foostan/crkbd/pcbs/common/right.kicad_sch

## KiCad design pcbs/common/right.kicad_sch (2024-05-06)

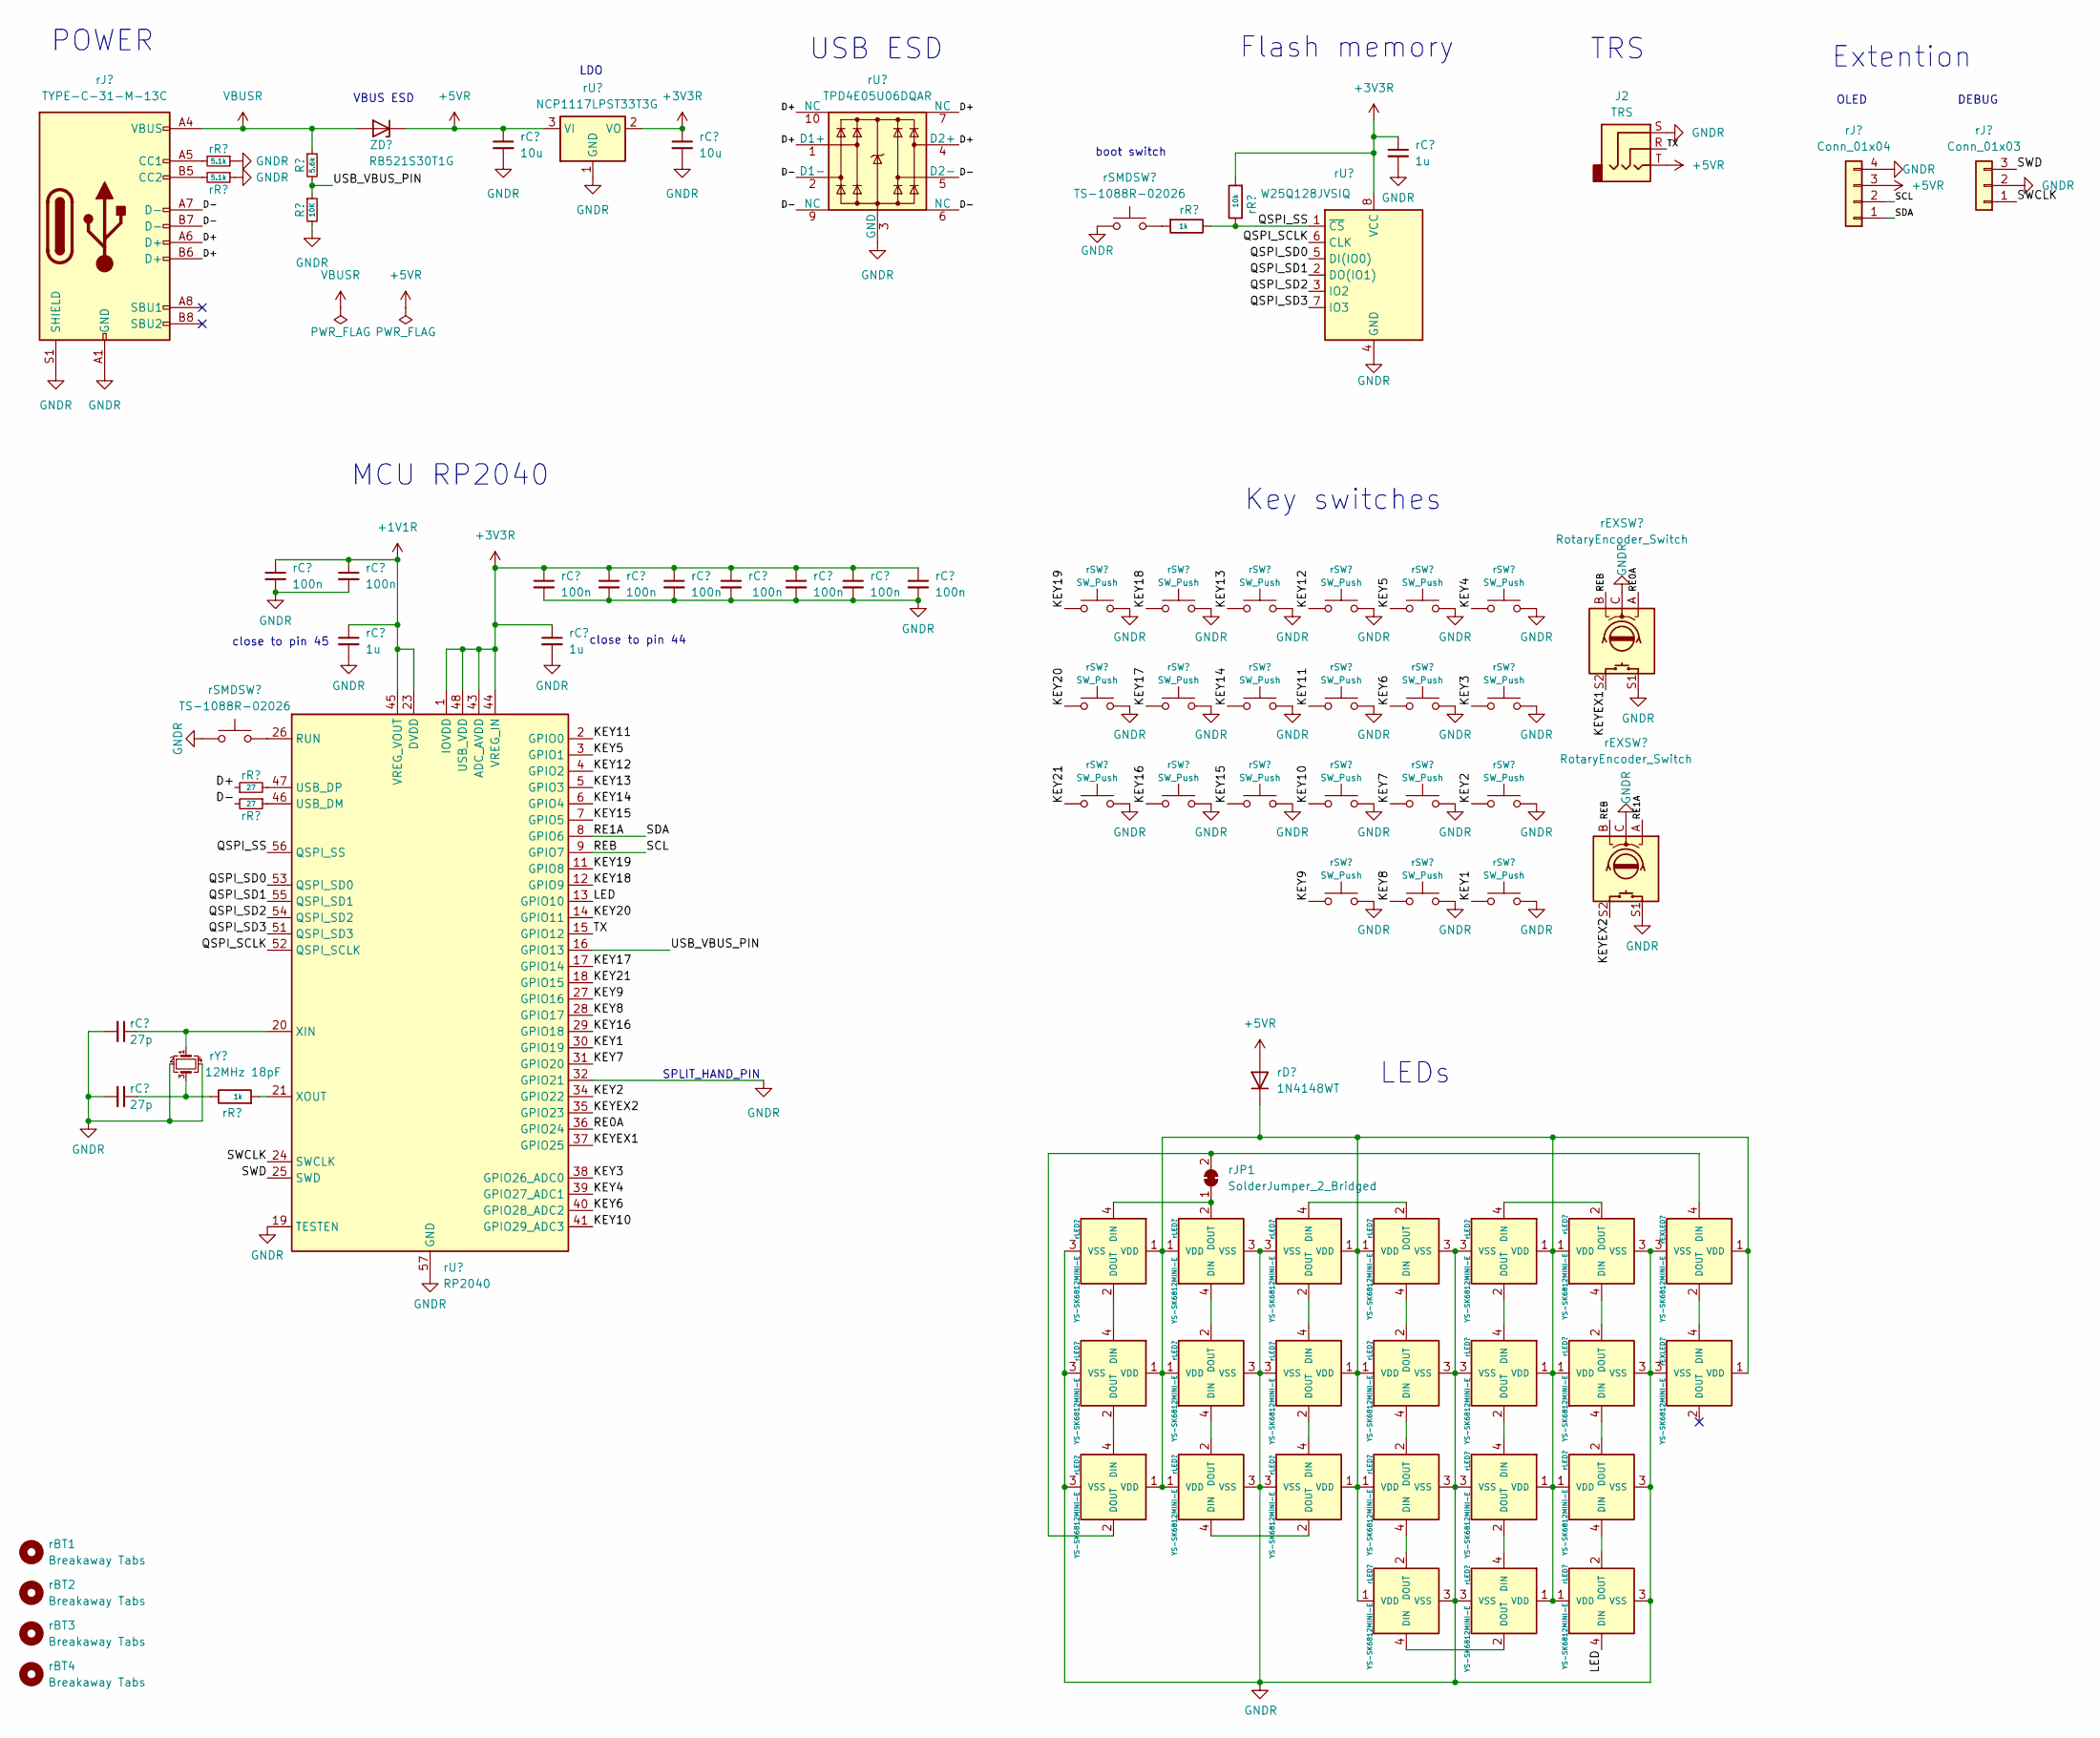
[picture p46: schematic right.kicad_sch]

Parts:
J2: TRS; PJ-398A-5A_PJ-399B-6A; JLCPCB Part # C128994
R8: 5.6k; R_0402_1005Metric
R9: 10K; R_0402_1005Metric
ZD1: RB521S30T1G; D_SOD-523; JLCPCB Part # C145179
rBT1, rBT2, rBT3, rBT4: Breakaway Tabs; Breakaway_Tabs
rC1, rC2: 27p; C_0402_1005Metric
rC3, rC4, rC7, rC9, rC10, rC12, rC13, rC14, rC15: 100n; C_0402_1005Metric
rC5, rC8, rC16: 1u; C_0402_1005Metric
rC6, rC11: 10u; C_0402_1005Metric
rD1: 1N4148WT; D_SOD-523; JLCPCB Part # C232841
rEXLED1, rEXLED2: YS-SK6812MINI-E
rEXSW1, rEXSW2: RotaryEncoder_Switch; keyswitch_cherrymx_hotswap_1u_rotary_encoder_ec12
rJ1: TYPE-C-31-M-13C; JLCPCB Part # C2848620
rJ3: Conn_01x04; OLED
rJ4: Conn_01x03; PinHeader_1x03_P2.54mm_Vertical
rJP1: SolderJumper_2_Bridged; SolderJumper-2_P1.3mm_Open_RoundedPad1.0x1.5mm
rLED1, rLED2, rLED3, rLED4, rLED5, rLED6, rLED7, rLED8, rLED9, rLED10, rLED11, rLED12, rLED13, rLED14, rLED15, rLED16, rLED17, rLED18, rLED19, rLED20, rLED21: YS-SK6812MINI-E
rR1, rR2: 5.1k; R_0402_1005Metric
rR3, rR6: 1k; R_0402_1005Metric
rR4, rR5: 27; R_0402_1005Metric
rR7: 10k; R_0402_1005Metric
rSMDSW1, rSMDSW2: TS-1088R-02026; JLCPCB Part # C455280
rSW1: SW_Push; keyswitch_cherrymx_hotswap_1.5u
rSW2, rSW3, rSW4, rSW5, rSW6, rSW7, rSW8, rSW9, rSW10, rSW11, rSW12, rSW13, rSW14, rSW15, rSW16, rSW17, rSW18, rSW19, rSW20, rSW21: SW_Push; keyswitch_cherrymx_hotswap_1u
rU1: RP2040; QFN-56-1EP_7x7mm_P0.4mm_EP3.2x3.2mm; JLCPCB Part # C2040
rU2: NCP1117LPST33T3G; SOT-223-3_TabPin2; JLCPCB Part # C146799
rU3: TPD4E05U06DQAR; USON-10_2.5x1.0mm_P0.5mm; JLCPCB Part # C138714
rU4: W25Q128JVSIQ; SOIC-8_5.23x5.23mm_P1.27mm; JLCPCB Part # C113767
rY1: 12MHz 18pF; Crystal_SMD_3225-4Pin_3.2x2.5mm; MFR.Part # Q22FA23V0041800; JLCPCB Part # C91749

Connections:
+1V1R: rC3.1, rC4.1, rC5.1, rU1.23 (DVDD), rU1.45 (VREG_VOUT), rU1.50 (DVDD)
+3V3R: rC7.1, rC8.1, rC9.1, rC10.1, rC11.1, rC12.1, rC13.1, rC14.1, rC15.1, rC16.1, rR7.2, rU1.1 (IOVDD), rU1.10 (IOVDD), rU1.22 (IOVDD), rU1.33 (IOVDD), rU1.42 (IOVDD), rU1.43 (ADC_AVDD), rU1.44 (VREG_IN), rU1.48 (USB_VDD), rU1.49 (IOVDD), rU2.2 (VO), rU4.8 (VCC)
+5VR: J2.T, ZD1.1 (K), rC6.1, rD1.2 (A), rJ3.3, rU2.3 (VI)
D+: rJ1.A6 (D+), rJ1.B6 (D+), rR4.1, rU3.1 (D1+), rU3.4 (D2+), rU3.7 (NC), rU3.10 (NC)
D-: rJ1.A7 (D-), rJ1.B7 (D-), rR5.2, rU3.2 (D1-), rU3.5 (D2-), rU3.6 (NC), rU3.9 (NC)
GNDR: J2.S, R9.2, rC1.2, rC2.2, rC3.2, rC4.2, rC5.2, rC6.2, rC7.2, rC8.2, rC9.2, rC10.2, rC11.2, rC12.2, rC13.2, rC14.2, rC15.2, rC16.2, rEXLED1.3 (VSS), rEXLED2.3 (VSS), rEXSW1.C, rEXSW1.S1, rEXSW2.C, rEXSW2.S1, rJ1.A1 (GND), rJ1.A12 (GND), rJ1.B1 (GND), rJ1.B12 (GND), rJ1.S1 (SHIELD), rJ3.4, rJ4.2, rLED1.3 (VSS), rLED2.3 (VSS), rLED3.3 (VSS), rLED4.3 (VSS), rLED5.3 (VSS), rLED6.3 (VSS), rLED7.3 (VSS), rLED8.3 (VSS), rLED9.3 (VSS), rLED10.3 (VSS), rLED11.3 (VSS), rLED12.3 (VSS), rLED13.3 (VSS), rLED14.3 (VSS), rLED15.3 (VSS), rLED16.3 (VSS), rLED17.3 (VSS), rLED18.3 (VSS), rLED19.3 (VSS), rLED20.3 (VSS), rLED21.3 (VSS), rR1.1, rR2.1, rSMDSW1.1, rSMDSW2.1, rSW1.2, rSW2.2, rSW3.2, rSW4.2, rSW5.2, rSW6.2, rSW7.2, rSW8.2, rSW9.2, rSW10.2, rSW11.2, rSW12.2, rSW13.2, rSW14.2, rSW15.2, rSW16.2, rSW17.2, rSW18.2, rSW19.2, rSW20.2, rSW21.2, rU1.19 (TESTEN), rU1.32 (GPIO21), rU1.57 (GND), rU2.1 (GND), rU3.3 (GND), rU3.8 (GND), rU4.4 (GND), rY1.2, rY1.4
KEY1: rSW1.1, rU1.30 (GPIO19)
KEY2: rSW2.1, rU1.34 (GPIO22)
KEY3: rSW3.1, rU1.38 (GPIO26_ADC0)
KEY4: rSW4.1, rU1.39 (GPIO27_ADC1)
KEY5: rSW5.1, rU1.3 (GPIO1)
KEY6: rSW6.1, rU1.40 (GPIO28_ADC2)
KEY7: rSW7.1, rU1.31 (GPIO20)
KEY8: rSW8.1, rU1.28 (GPIO17)
KEY9: rSW9.1, rU1.27 (GPIO16)
KEY10: rSW10.1, rU1.41 (GPIO29_ADC3)
KEY11: rSW11.1, rU1.2 (GPIO0)
KEY12: rSW12.1, rU1.4 (GPIO2)
KEY13: rSW13.1, rU1.5 (GPIO3)
KEY14: rSW14.1, rU1.6 (GPIO4)
KEY15: rSW15.1, rU1.7 (GPIO5)
KEY16: rSW16.1, rU1.29 (GPIO18)
KEY17: rSW17.1, rU1.17 (GPIO14)
KEY18: rSW18.1, rU1.12 (GPIO9)
KEY19: rSW19.1, rU1.11 (GPIO8)
KEY20: rSW20.1, rU1.14 (GPIO11)
KEY21: rSW21.1, rU1.18 (GPIO15)
KEYEX1: rEXSW1.S2, rU1.37 (GPIO25)
KEYEX2: rEXSW2.S2, rU1.35 (GPIO23)
LED: rLED1.4 (DIN), rU1.13 (GPIO10)
unnamed: rC1.1, rU1.20 (XIN), rY1.1
unnamed: rC2.1, rR3.1, rY1.3
unnamed: rD1.1 (K), rEXLED1.1 (VDD), rEXLED2.1 (VDD), rLED1.1 (VDD), rLED2.1 (VDD), rLED3.1 (VDD), rLED4.1 (VDD), rLED5.1 (VDD), rLED6.1 (VDD), rLED7.1 (VDD), rLED8.1 (VDD), rLED9.1 (VDD), rLED10.1 (VDD), rLED11.1 (VDD), rLED12.1 (VDD), rLED13.1 (VDD), rLED14.1 (VDD), rLED15.1 (VDD), rLED16.1 (VDD), rLED17.1 (VDD), rLED18.1 (VDD), rLED19.1 (VDD), rLED20.1 (VDD), rLED21.1 (VDD)
unnamed: rEXLED1.2 (DOUT), rEXLED2.4 (DIN)
unnamed: rEXLED1.4 (DIN), rJP1.2 (B), rLED21.2 (DOUT)
unnamed: rJ1.A5 (CC1), rR1.2
unnamed: rJ1.B5 (CC2), rR2.2
unnamed: rJP1.1 (A), rLED18.2 (DOUT), rLED19.4 (DIN)
unnamed: rLED1.2 (DOUT), rLED2.4 (DIN)
unnamed: rLED2.2 (DOUT), rLED3.4 (DIN)
unnamed: rLED3.2 (DOUT), rLED4.4 (DIN)
unnamed: rLED4.2 (DOUT), rLED5.4 (DIN)
unnamed: rLED5.2 (DOUT), rLED6.4 (DIN)
unnamed: rLED6.2 (DOUT), rLED7.4 (DIN)
unnamed: rLED7.2 (DOUT), rLED8.4 (DIN)
unnamed: rLED8.2 (DOUT), rLED9.4 (DIN)
unnamed: rLED10.2 (DOUT), rLED11.4 (DIN)
unnamed: rLED9.2 (DOUT), rLED10.4 (DIN)
unnamed: rLED11.2 (DOUT), rLED12.4 (DIN)
unnamed: rLED12.2 (DOUT), rLED13.4 (DIN)
unnamed: rLED13.2 (DOUT), rLED14.4 (DIN)
unnamed: rLED14.2 (DOUT), rLED15.4 (DIN)
unnamed: rLED15.2 (DOUT), rLED16.4 (DIN)
unnamed: rLED16.2 (DOUT), rLED17.4 (DIN)
unnamed: rLED17.2 (DOUT), rLED18.4 (DIN)
unnamed: rLED19.2 (DOUT), rLED20.4 (DIN)
unnamed: rLED20.2 (DOUT), rLED21.4 (DIN)
unnamed: rR3.2, rU1.21 (XOUT)
unnamed: rR4.2, rU1.47 (USB_DP)
unnamed: rR5.1, rU1.46 (USB_DM)
unnamed: rR6.2, rSMDSW1.2
unnamed: rSMDSW2.2, rU1.26 (RUN)
QSPI_SCLK: rU1.52 (QSPI_SCLK), rU4.6 (CLK)
QSPI_SD0: rU1.53 (QSPI_SD0), rU4.5 (DI(IO0))
QSPI_SD1: rU1.55 (QSPI_SD1), rU4.2 (DO(IO1))
QSPI_SD2: rU1.54 (QSPI_SD2), rU4.3 (IO2)
QSPI_SD3: rU1.51 (QSPI_SD3), rU4.7 (IO3)
QSPI_SS: rR6.1, rR7.1, rU1.56 (QSPI_SS), rU4.1 (~CS)
RE0A: rEXSW1.A, rU1.36 (GPIO24)
RE1A: rEXSW2.A, rJ3.1, rU1.8 (GPIO6)
REB: rEXSW1.B, rEXSW2.B, rJ3.2, rU1.9 (GPIO7)
SWCLK: rJ4.1, rU1.24 (SWCLK)
SWD: rJ4.3, rU1.25 (SWD)
TX: J2.R, rU1.15 (GPIO12)
USB_VBUS_PIN: R8.2, R9.1, rU1.16 (GPIO13)
VBUSR: R8.1, ZD1.2 (A), rJ1.A4 (VBUS), rJ1.A9 (VBUS), rJ1.B4 (VBUS), rJ1.B9 (VBUS)

Notes on the sheet:
USB ESD
TRS
Flash memory
MCU RP2040
DEBUG
POWER
boot switch
LDO
Key switches
LEDs
Extention
VBUS ESD
OLED
close to pin 45
close to pin 44
SPLIT_HAND_PIN
